dmweis/Hopper_ROS/images/first_hopper.jpg

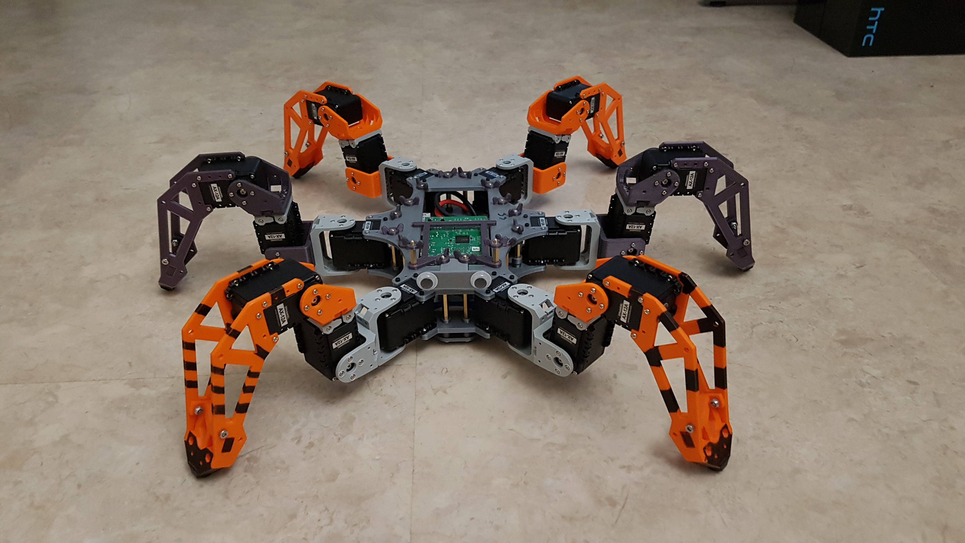
images/first_hopper.jpg
