dmweis/Hopper_ROS/hopper_feet_sensors/src/feet_sensor_controller.py

#!/usr/bin/env python

from __future__ import print_function, division

import serial
import rospy

from hopper_feet_sensors.msg import FeetSensorData


class FeetSensor(object):
    def __init__(self):
        super(FeetSensor, self).__init__()
        rospy.init_node("feet_sensors")
        self.feet_publisher = rospy.Publisher("hopper/feet", FeetSensorData, queue_size=10)
        with serial.Serial('/dev/hopper_feet', 9600) as port:
            port.timeout = 1
            while not rospy.is_shutdown():
                data = port.readline().strip().split(' ')
                if len(data) == 6:
                    new_msg = FeetSensorData()
                    new_msg.left_front = bool(int(data[5]))
                    new_msg.right_front = bool(int(data[0]))
                    new_msg.left_middle = bool(int(data[3]))
                    new_msg.right_middle = bool(int(data[2]))
                    new_msg.left_rear = bool(int(data[4]))
                    new_msg.right_rear = bool(int(data[1]))
                    self.feet_publisher.publish(new_msg)
                else:
                    rospy.logdebug("String format error")


if __name__ == "__main__":
    FeetSensor()
