dmweis/Hopper_ROS/hopper_controller/src/hopper_leg_position_reader_node.py

#!/usr/bin/env python

from __future__ import division
import rospy
from ros_abstraction import IkController
from geometry_msgs.msg import Point, Vector3
from std_msgs.msg import ColorRGBA
from visualization_msgs.msg import Marker


def create_marker_for_feet(leg_positions):
    marker = Marker()
    marker.header.frame_id = "body_link"
    marker.header.stamp = rospy.Time.now()
    marker.type = Marker.POINTS
    marker.action = Marker.ADD
    marker.pose.orientation.w = 1.
    marker.scale = Vector3(0.02, 0.02, 0.02)
    marker.lifetime = rospy.Duration(0)
    marker.frame_locked = True

    def vector_to_point(vector):
        return Point(vector.x / 100, vector.y / 100, vector.z / 100)
    marker.points.append(vector_to_point(leg_positions.left_front))
    marker.points.append(vector_to_point(leg_positions.right_front))
    marker.points.append(vector_to_point(leg_positions.left_middle))
    marker.points.append(vector_to_point(leg_positions.right_middle))
    marker.points.append(vector_to_point(leg_positions.left_rear))
    marker.points.append(vector_to_point(leg_positions.right_rear))
    for i in range(6):
        marker.colors.append(ColorRGBA(0, 1, 0, 1))
    return marker


class LegPositionReader(object):
    def __init__(self):
        super(LegPositionReader, self).__init__()
        rospy.init_node("hopper_leg_position_reader")
        marker_publisher = rospy.Publisher("hopper/feet/markers", Marker, queue_size=10)
        ik_controller = IkController()
        ik_controller.disable_motors()
        loop_rate = rospy.Rate(30)
        while not rospy.is_shutdown():
            leg_positions = ik_controller.read_current_leg_positions()
            markers = create_marker_for_feet(leg_positions)
            marker_publisher.publish(markers)
            loop_rate.sleep()


if __name__ == "__main__":
    LegPositionReader()
