dmweis/Hopper_ROS/hopper_controller/src/dynamixel/dynamixel_functions.py

#!/usr/bin/env python
# -*- coding: utf-8 -*-

################################################################################
# Copyright 2017 ROBOTIS CO., LTD.
#
# Licensed under the Apache License, Version 2.0 (the "License");
# you may not use this file except in compliance with the License.
# You may obtain a copy of the License at
#
#     http://www.apache.org/licenses/LICENSE-2.0
#
# Unless required by applicable law or agreed to in writing, software
# distributed under the License is distributed on an "AS IS" BASIS,
# WITHOUT WARRANTIES OR CONDITIONS OF ANY KIND, either express or implied.
# See the License for the specific language governing permissions and
# limitations under the License.
################################################################################

# Author: Ryu Woon Jung (Leon)

import ctypes
from ctypes import cdll
from os import path

import platform

local_path = path.dirname(__file__)
library_path = ""
if 'Windows' in platform.platform():
    if '32' in platform.architecture()[0]:
        library_path = path.join(local_path, "dxl_x86_c.dll")
    elif '64' in platform.architecture()[0]:
        library_path = path.join(local_path, "dxl_x64_c.dll")
elif 'Linux' in platform.platform():
    if 'arm' in platform.platform():
        library_path = path.join(local_path, "libdxl_sbc_c.so")
    elif '32' in platform.architecture()[0]:
        library_path = path.join(local_path, "libdxl_x86_c.so")
    elif '64' in platform.architecture()[0]:
        library_path = path.join(local_path, "libdxl_sbc64_c.so")
dxl_lib = cdll.LoadLibrary(library_path)
# dxl_lib = cdll.LoadLibrary("./libdxl_mac_c.dylib")  # for Mac OS

# port_handler
portHandler = dxl_lib.portHandler

openPort = dxl_lib.openPort
closePort = dxl_lib.closePort
clearPort = dxl_lib.clearPort

setPortName = dxl_lib.setPortName
getPortName = dxl_lib.getPortName

setBaudRate = dxl_lib.setBaudRate
getBaudRate = dxl_lib.getBaudRate

readPort = dxl_lib.readPort
writePort = dxl_lib.writePort

setPacketTimeout = dxl_lib.setPacketTimeout
setPacketTimeoutMSec = dxl_lib.setPacketTimeoutMSec
isPacketTimeout = dxl_lib.isPacketTimeout

# packet_handler
packetHandler = dxl_lib.packetHandler

getTxRxResult = dxl_lib.getTxRxResult
getTxRxResult.restype = ctypes.c_int
getRxPacketError = dxl_lib.getRxPacketError
getRxPacketError.restype = ctypes.c_byte

getLastTxRxResult = dxl_lib.getLastTxRxResult
getLastTxRxResult.restype = ctypes.c_int
getLastRxPacketError = dxl_lib.getLastRxPacketError
getLastRxPacketError.restype = ctypes.c_byte


setDataWrite = dxl_lib.setDataWrite
getDataRead = dxl_lib.getDataRead

txPacket = dxl_lib.txPacket

rxPacket = dxl_lib.rxPacket

txRxPacket = dxl_lib.txRxPacket

ping = dxl_lib.ping

pingGetModelNum = dxl_lib.pingGetModelNum

broadcastPing = dxl_lib.broadcastPing
getBroadcastPingResult = dxl_lib.getBroadcastPingResult

reboot = dxl_lib.reboot

factoryReset = dxl_lib.factoryReset

readTx = dxl_lib.readTx
readRx = dxl_lib.readRx
readTxRx = dxl_lib.readTxRx

read1ByteTx = dxl_lib.read1ByteTx
read1ByteRx = dxl_lib.read1ByteRx
read1ByteTxRx = dxl_lib.read1ByteTxRx
read1ByteTxRx.restype = ctypes.c_ubyte

read2ByteTx = dxl_lib.read2ByteTx
read2ByteRx = dxl_lib.read2ByteRx
read2ByteTxRx = dxl_lib.read2ByteTxRx

read4ByteTx = dxl_lib.read4ByteTx
read4ByteRx = dxl_lib.read4ByteRx
read4ByteTxRx = dxl_lib.read4ByteTxRx

writeTxOnly = dxl_lib.writeTxOnly
writeTxRx = dxl_lib.writeTxRx

write1ByteTxOnly = dxl_lib.write1ByteTxOnly
write1ByteTxRx = dxl_lib.write1ByteTxRx

write2ByteTxOnly = dxl_lib.write2ByteTxOnly
write2ByteTxRx = dxl_lib.write2ByteTxRx

write4ByteTxOnly = dxl_lib.write4ByteTxOnly
write4ByteTxRx = dxl_lib.write4ByteTxRx

regWriteTxOnly = dxl_lib.regWriteTxOnly
regWriteTxRx = dxl_lib.regWriteTxRx

syncReadTx = dxl_lib.syncReadTx
# syncReadRx   -> GroupSyncRead
# syncReadTxRx -> GroupSyncRead

syncWriteTxOnly = dxl_lib.syncWriteTxOnly

bulkReadTx = dxl_lib.bulkReadTx
# bulkReadRx   -> GroupBulkRead
# bulkReadTxRx -> GroupBulkRead

bulkWriteTxOnly = dxl_lib.bulkWriteTxOnly

# group_bulk_read
groupBulkRead = dxl_lib.groupBulkRead

groupBulkReadAddParam = dxl_lib.groupBulkReadAddParam
groupBulkReadRemoveParam = dxl_lib.groupBulkReadRemoveParam
groupBulkReadClearParam = dxl_lib.groupBulkReadClearParam

groupBulkReadTxPacket = dxl_lib.groupBulkReadTxPacket
groupBulkReadRxPacket = dxl_lib.groupBulkReadRxPacket
groupBulkReadTxRxPacket = dxl_lib.groupBulkReadTxRxPacket

groupBulkReadIsAvailable = dxl_lib.groupBulkReadIsAvailable
groupBulkReadGetData = dxl_lib.groupBulkReadGetData

#group_bulk_write
groupBulkWrite = dxl_lib.groupBulkWrite

groupBulkWriteAddParam = dxl_lib.groupBulkWriteAddParam
groupBulkWriteRemoveParam = dxl_lib.groupBulkWriteRemoveParam
groupBulkWriteChangeParam = dxl_lib.groupBulkWriteChangeParam
groupBulkWriteClearParam = dxl_lib.groupBulkWriteClearParam

groupBulkWriteTxPacket = dxl_lib.groupBulkWriteTxPacket

#group_sync_read
groupSyncRead = dxl_lib.groupSyncRead

groupSyncReadAddParam = dxl_lib.groupSyncReadAddParam
groupSyncReadRemoveParam = dxl_lib.groupSyncReadRemoveParam
groupSyncReadClearParam = dxl_lib.groupSyncReadClearParam

groupSyncReadTxPacket = dxl_lib.groupSyncReadTxPacket
groupSyncReadRxPacket = dxl_lib.groupSyncReadRxPacket
groupSyncReadTxRxPacket = dxl_lib.groupSyncReadTxRxPacket

groupSyncReadIsAvailable = dxl_lib.groupSyncReadIsAvailable
groupSyncReadGetData = dxl_lib.groupSyncReadGetData

#group_sync_write
groupSyncWrite = dxl_lib.groupSyncWrite

groupSyncWriteAddParam = dxl_lib.groupSyncWriteAddParam
groupSyncWriteAddParam.argstypes = [ctypes.c_int32, ctypes.c_byte, ctypes.c_uint32, ctypes.c_uint16]
groupSyncWriteRemoveParam = dxl_lib.groupSyncWriteRemoveParam
groupSyncWriteChangeParam = dxl_lib.groupSyncWriteChangeParam
groupSyncWriteClearParam = dxl_lib.groupSyncWriteClearParam

groupSyncWriteTxPacket = dxl_lib.groupSyncWriteTxPacket
